jobvk/EPS-Weather-Station/Computer-Aided Design/Brick 300x300.SLDPRT

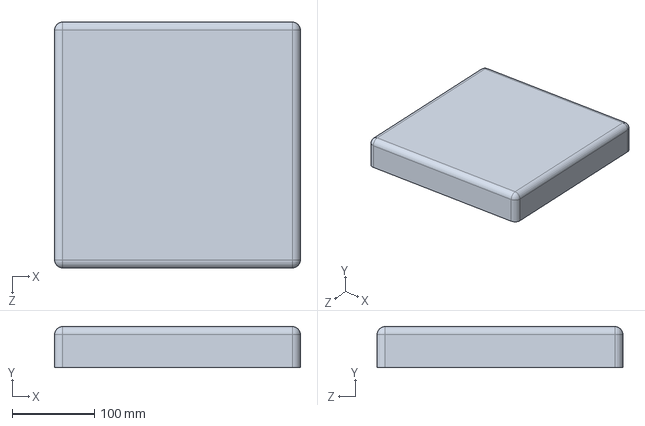
[picture p225: CAD file, 2022-12-19]
Computer-Aided Design/Brick 300x300.SLDPRT
300.0 x 50.0 x 300.0 mm
