jobvk/EPS-Weather-Station/Computer-Aided Design/L-beam.SLDPRT

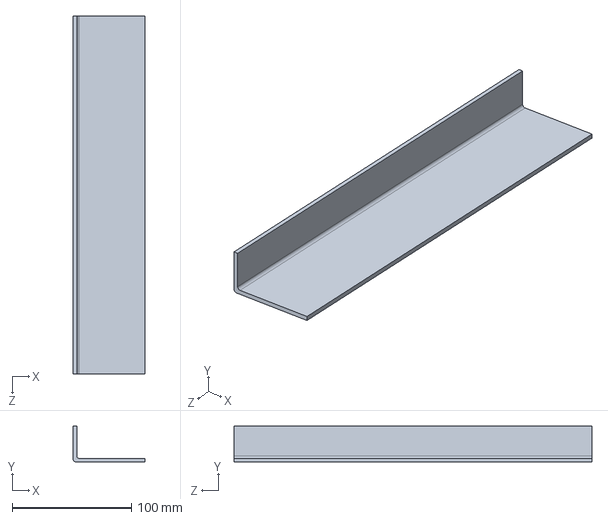
[picture p226: CAD file, 2022-12-19]
Computer-Aided Design/L-beam.SLDPRT
60.0 x 30.0 x 300.0 mm
