jobvk/EPS-Weather-Station/Computer-Aided Design/Wood pole 100x100x2200.SLDPRT

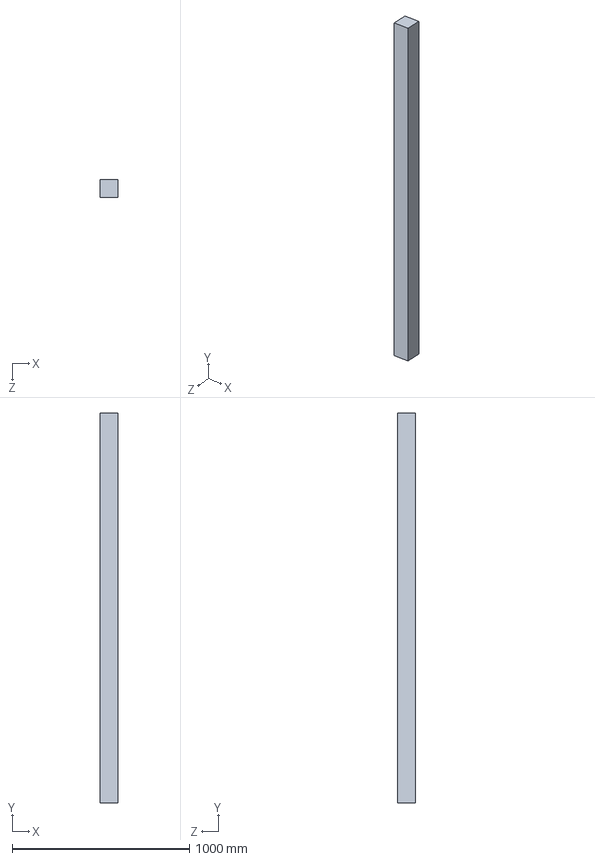
[picture p227: CAD file, 2022-12-19]
Computer-Aided Design/Wood pole 100x100x2200.SLDPRT
100.0 x 2200.0 x 100.0 mm
