jobvk/EPS-Weather-Station/Computer-Aided Design/Base temp.SLDPRT

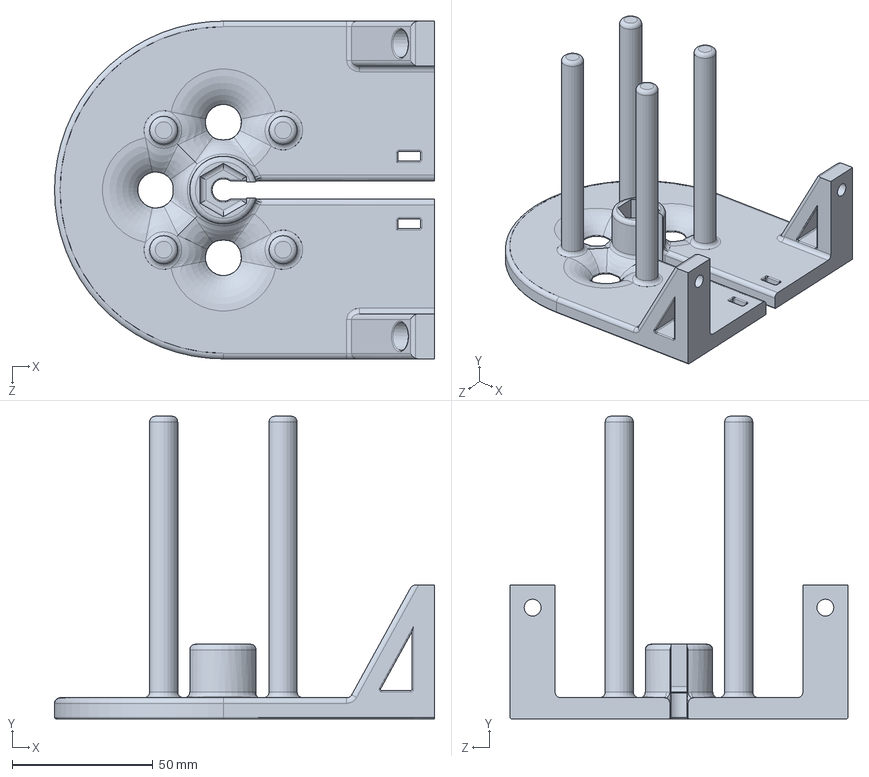
[picture p228: CAD file, 2022-12-19]
Computer-Aided Design/Base temp.SLDPRT
135.0 x 107.5 x 120.0 mm
