jobvk/EPS-Weather-Station/Computer-Aided Design/houder zonnepanneel v2.SLDPRT

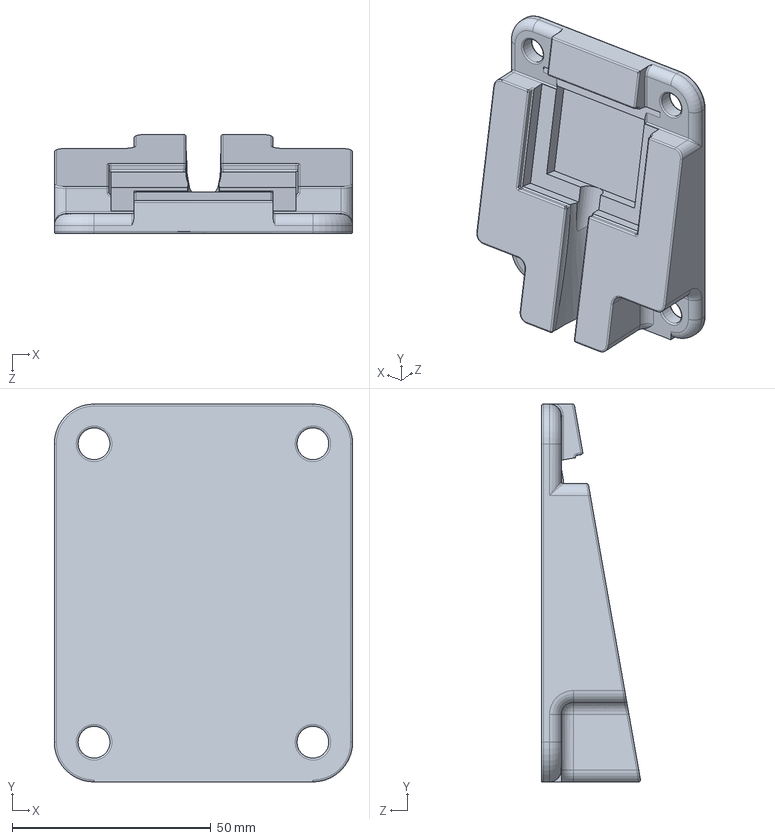
[picture p229: CAD file, 2022-12-19]
Computer-Aided Design/houder zonnepanneel v2.SLDPRT
75.0 x 95.0 x 24.9 mm
