jobvk/EPS-Weather-Station/Computer-Aided Design/Zonnepaneel.SLDPRT

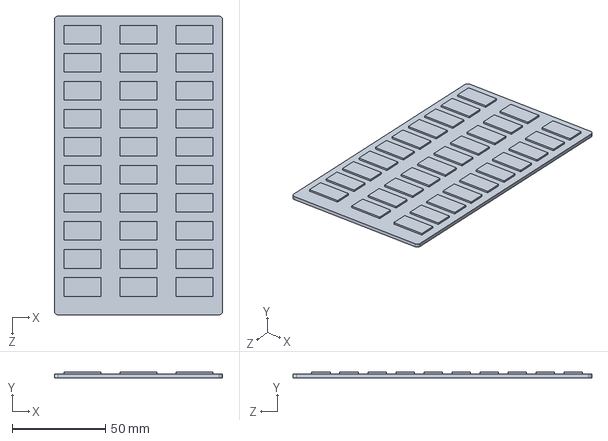
[picture p230: CAD file, 2022-12-19]
Computer-Aided Design/Zonnepaneel.SLDPRT
90.0 x 3.00 x 160.0 mm
