jobvk/EPS-Weather-Station/Computer-Aided Design/Mount V2.SLDPRT

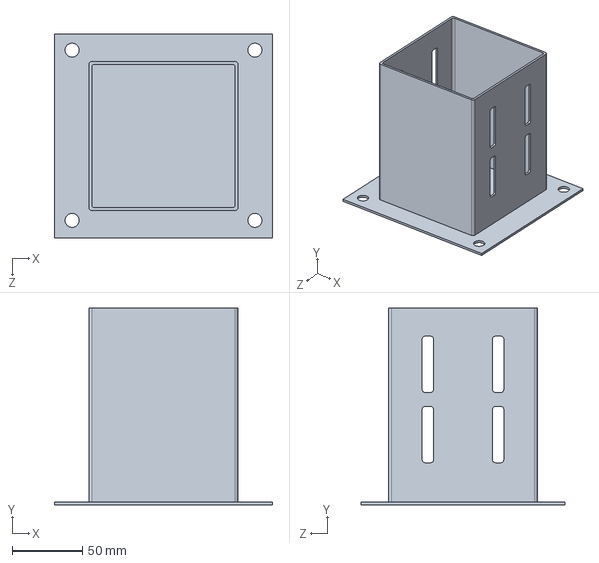
[picture p231: CAD file, 2022-12-19]
Computer-Aided Design/Mount V2.SLDPRT
155.0 x 140.0 x 145.0 mm
